wyolum/bebl_v2/kicad/data/conn_USB_cover_726291100.pdf

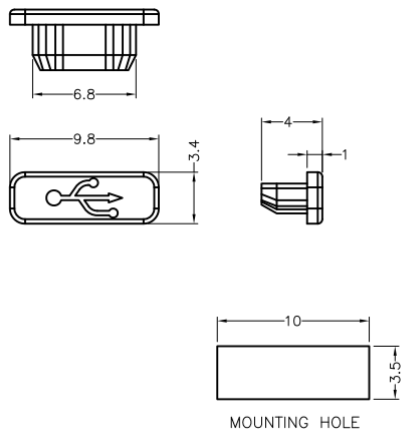
[picture p4: figure]

726291100 | Material: TPE
MICRO USB – Cover | Colour: black

Würth Elektronik eiSos GmbH & Co KG
D – 74638 Waldenburg
Max-Eyth-Straße 1
Tel.: 0049 7942-945-0 / Fax: 0049 7942-945-400

www.we-online.de
