wyolum/bebl_v2/kicad/images/bebl_v2_01.png

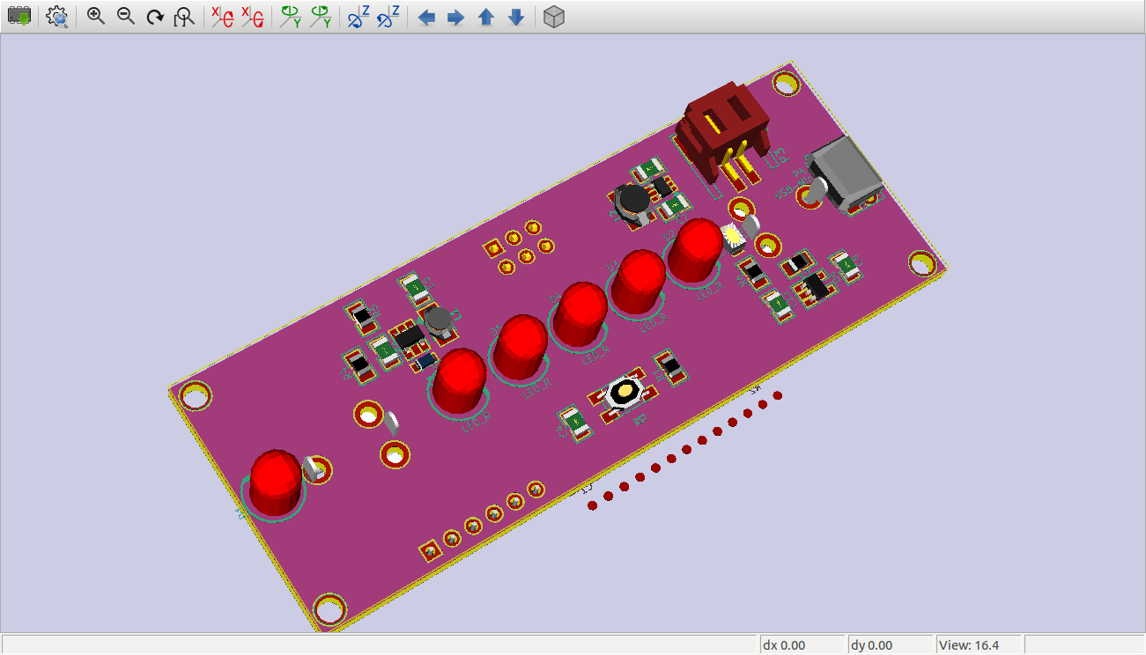
kicad/images/bebl_v2_01.png
