wyolum/bebl_v2/kicad/images/bebl_v2_02.png

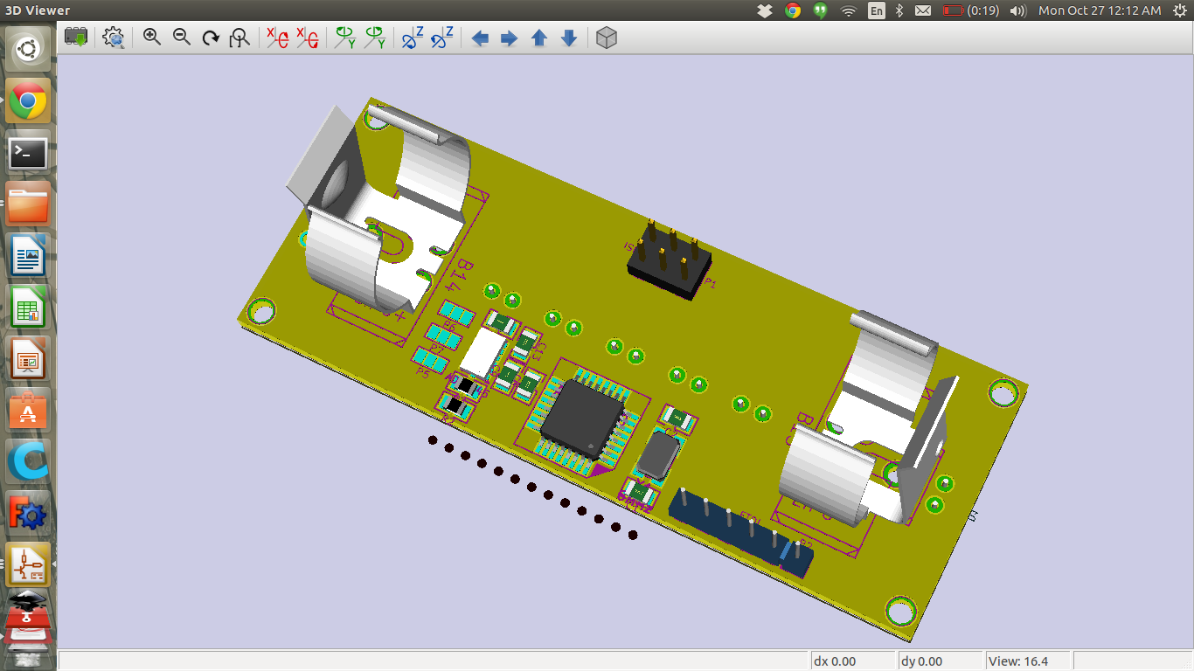
kicad/images/bebl_v2_02.png
