wyolum/bebl_v2/fabricate/old_archive/topcover.stl

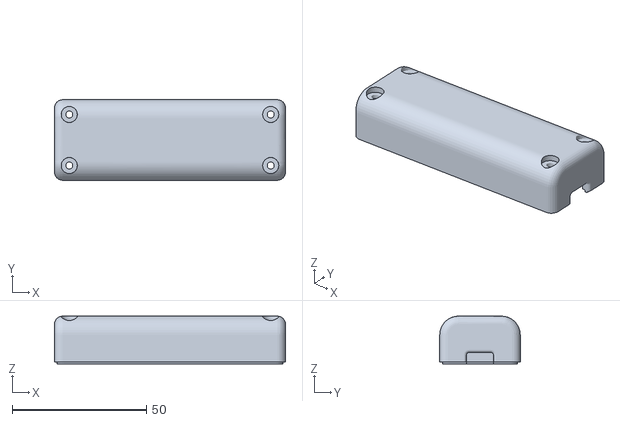
[picture p26: CAD file, 2014-11-03, an earlier design]
fabricate/old_archive/topcover.stl
86.0 x 30.0 x 17.8
