wyolum/bebl_v2/fabricate/bebl_v2_box03.png

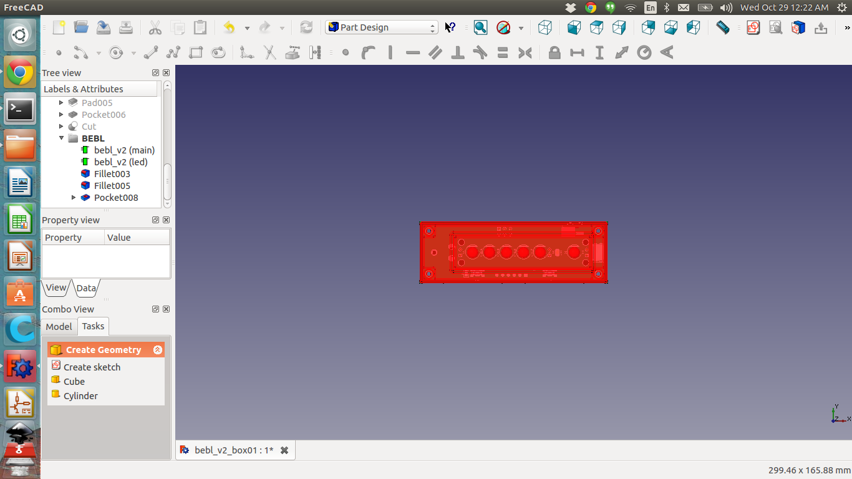
fabricate/bebl_v2_box03.png
