wyolum/bebl_v2/fabricate/bebl_v2_box4.png

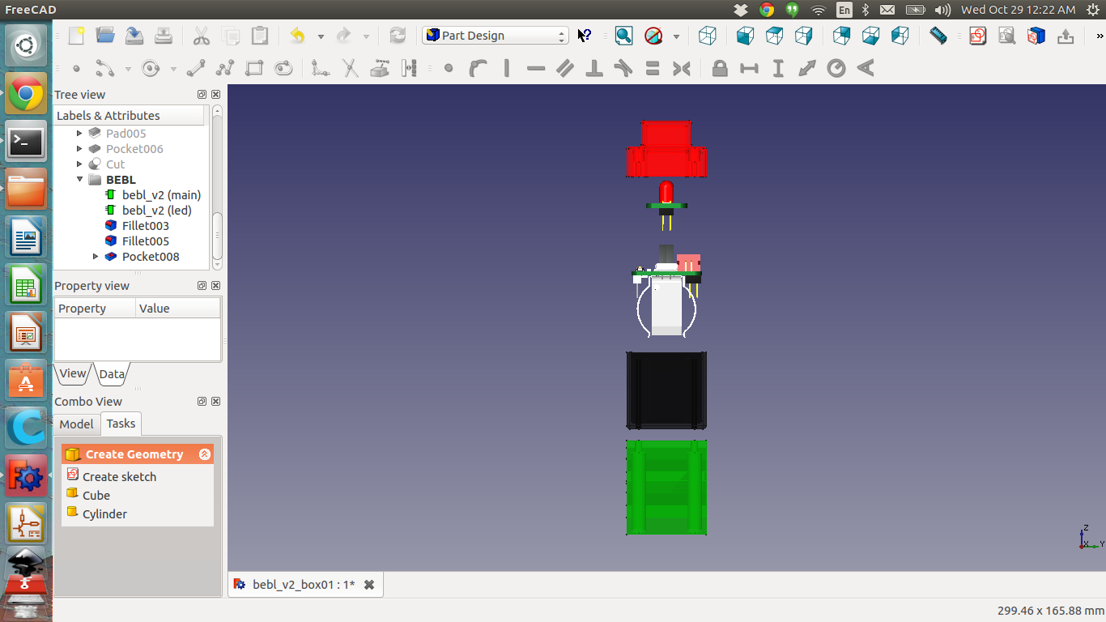
fabricate/bebl_v2_box4.png
