wyolum/bebl_v2/fabricate/bebl_v2_box05.png

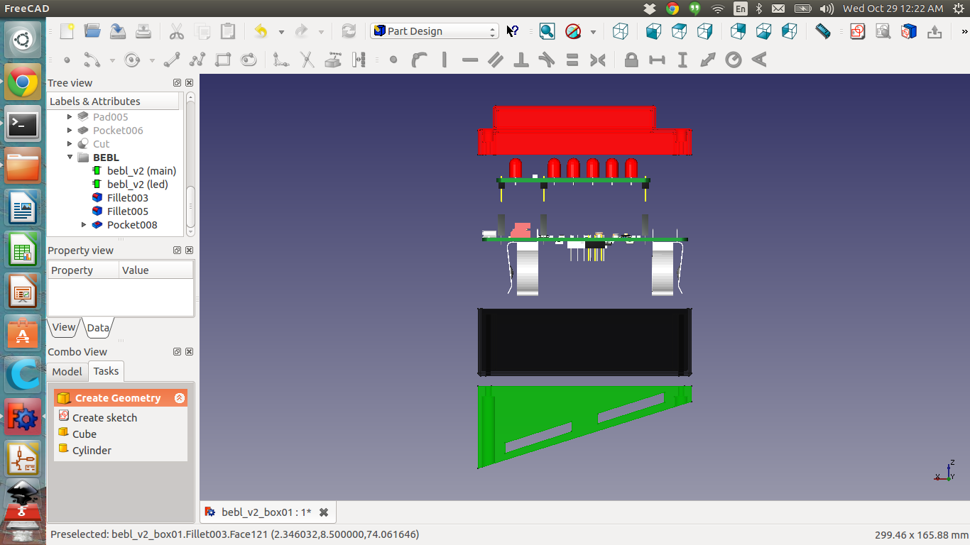
fabricate/bebl_v2_box05.png
