wyolum/bebl_v2/kicad/pdf/bebl_v2.pdf

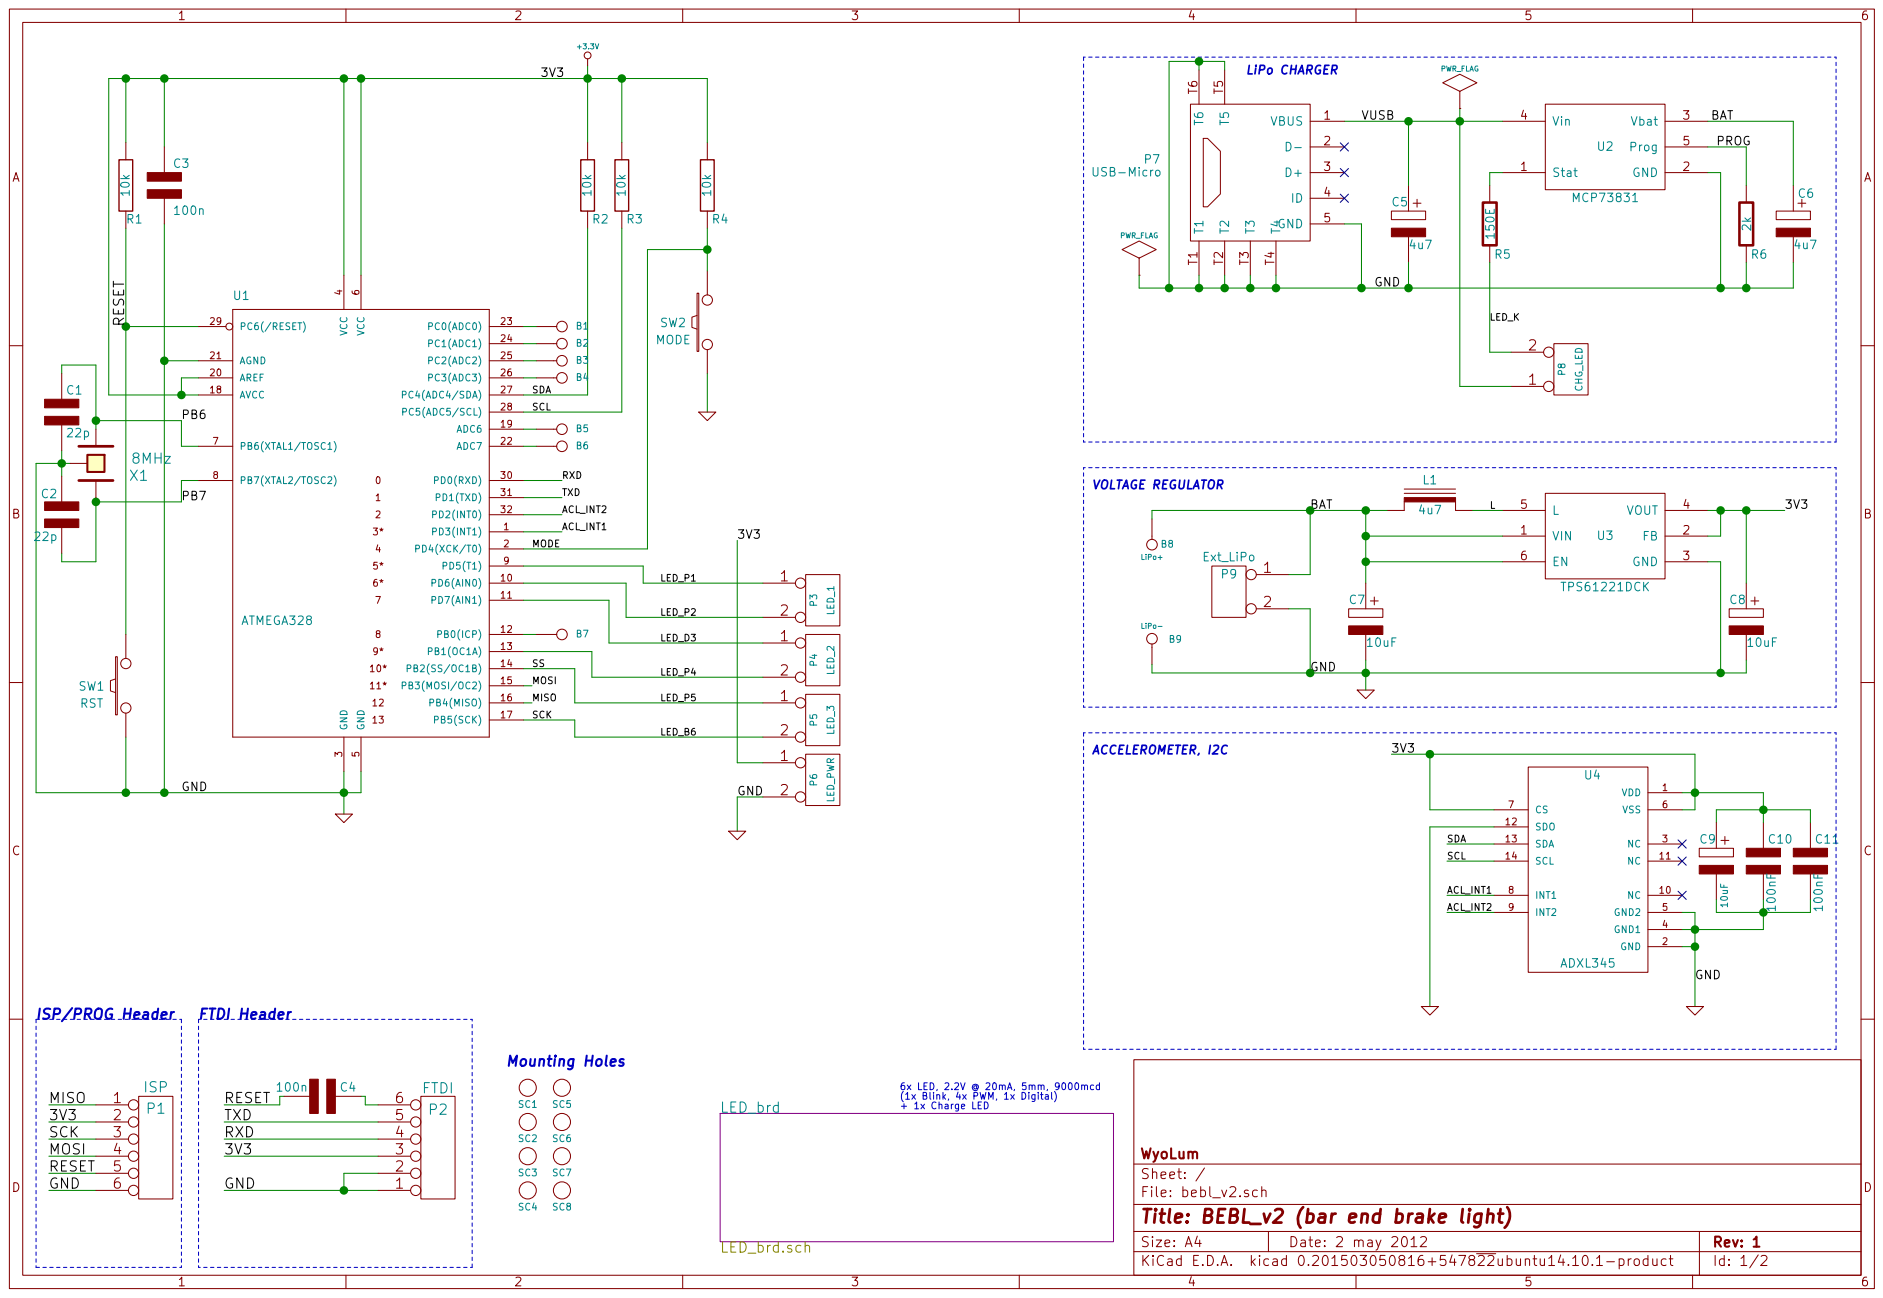
[picture p34: page 1]

6 PB6(XTAL1/TOSC1) 7 PB7(XTAL2/TOSC2) 8 PD5(T1) 9 PD6(AIN0) 10 AREF 20 PD0(RXD) 30 PD7(AIN1) 11 AGND 21 PD1(TXD) 31 PB0(ICP) 12 ADC7 22 PD2(INT0) 32 PB1(OC1A) 13 PC0(ADC0) 23 PB2(SS/OC1B) 14 PC1(ADC1) 24 PB3(MOSI/OC2) 15 PC2(ADC2) 25 PB4(MISO) 16 PC3(ADC3) 26 PB5(SCK) 17 PC4(ADC4/SDA) 27 AVCC 18 PC5(ADC5/SCL) 28 ADC6 19 PC6(/RESET) 29 U1ATMEGA328 X1

SDA
SCL SSMOSI SCK MISO

6x LED, 2.2V @ 20mA, 5mm, 9000mcd
(1x Blink, 4x PWM, 1x Digital) + 1x Charge LED

File: bebl_v2.sch Sheet: / WyoLum

Id: 1/2 Title: BEBL_v2 (bar end brake light)

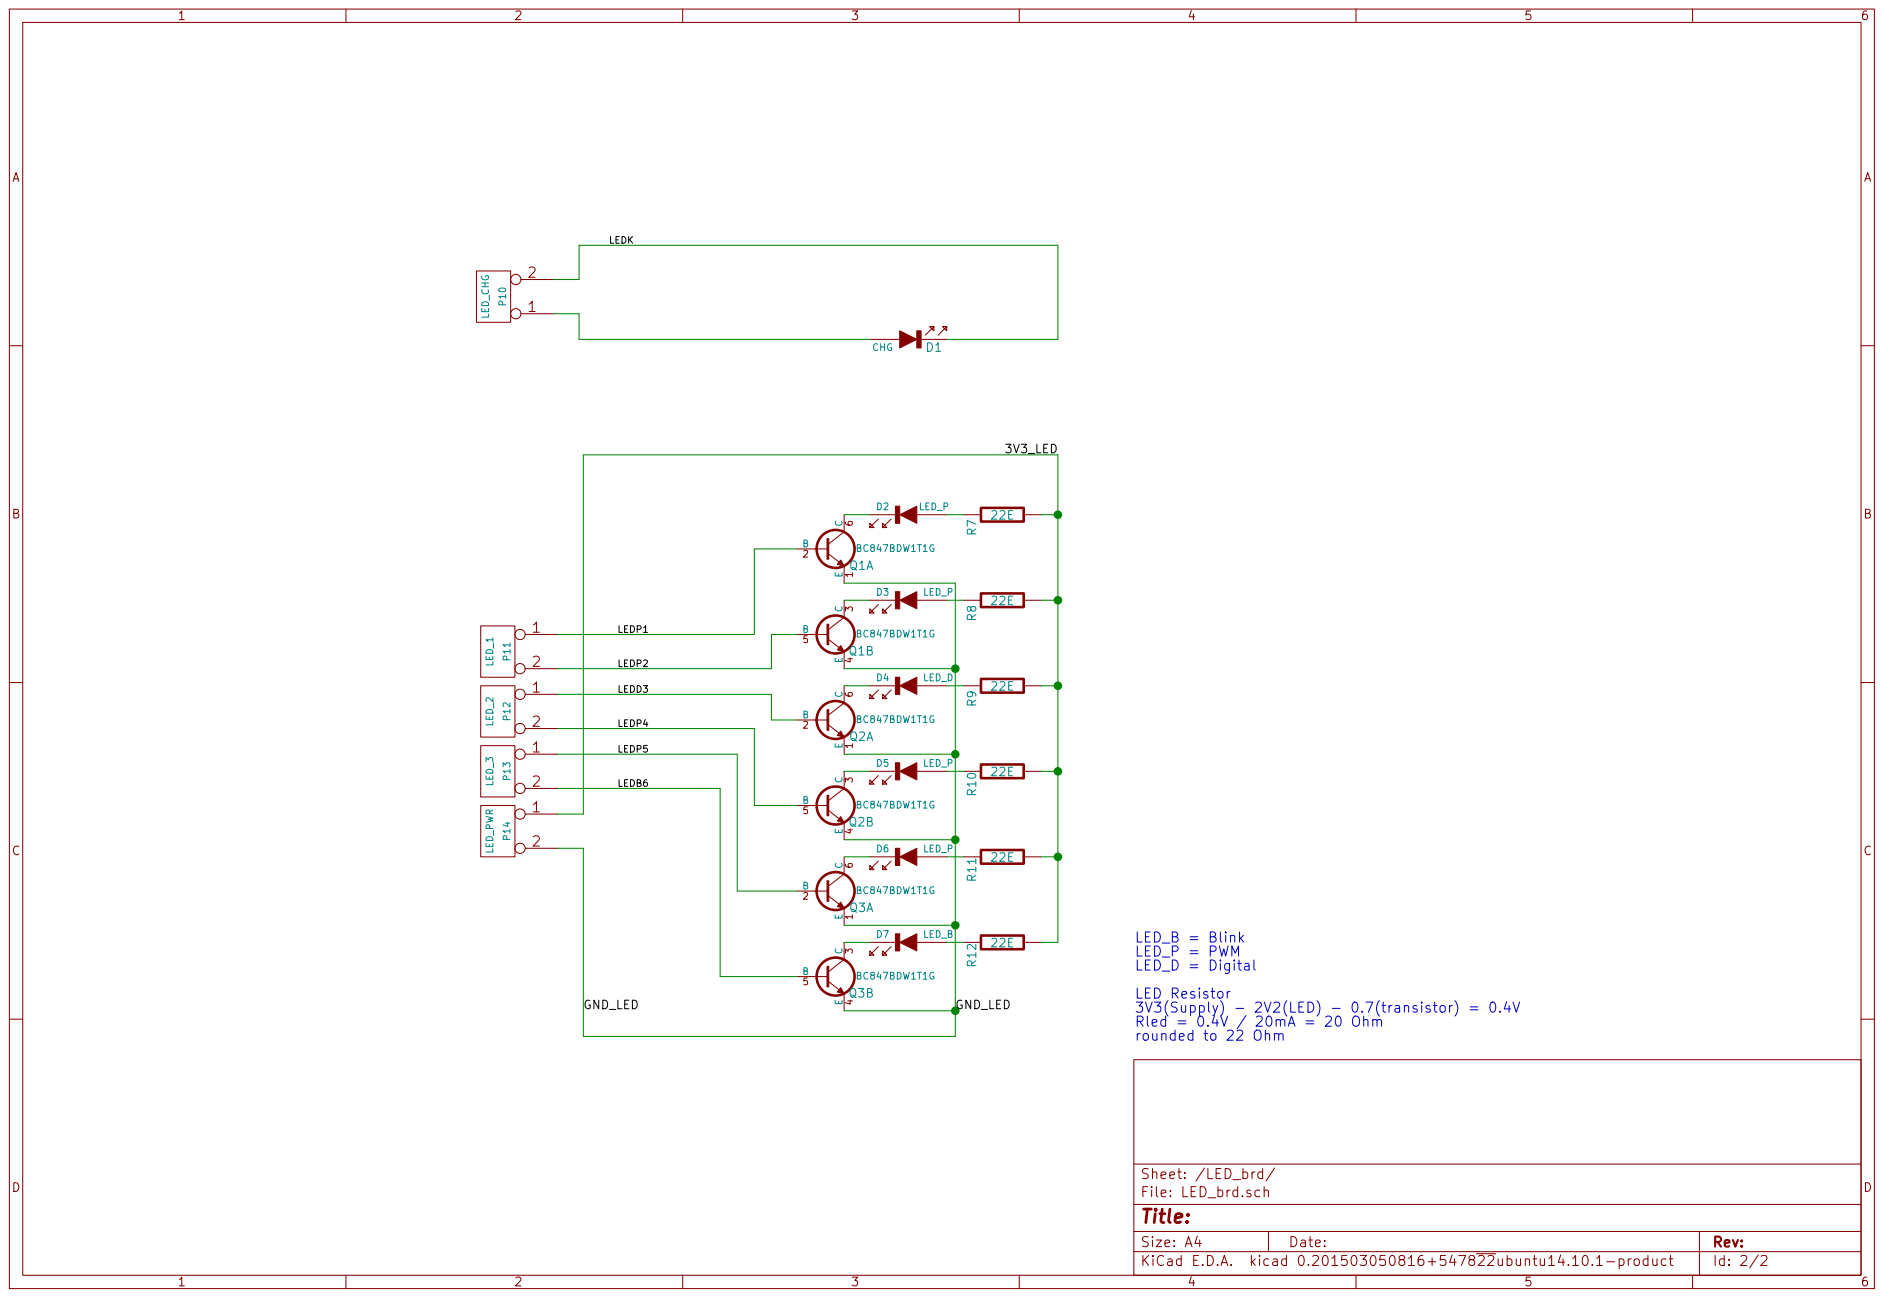
[picture p35: page 2]

LED_B = Blink
LED_P = PWM
LED_D = Digital LED Resistor 3V3(Supply) - 2V2(LED) - 0.7(transistor) = 0.4V Rled = 0.4V / 20mA = 20 Ohm
