wyolum/bebl_v2/kicad/images/bebl_v2_mockup_01.pdf

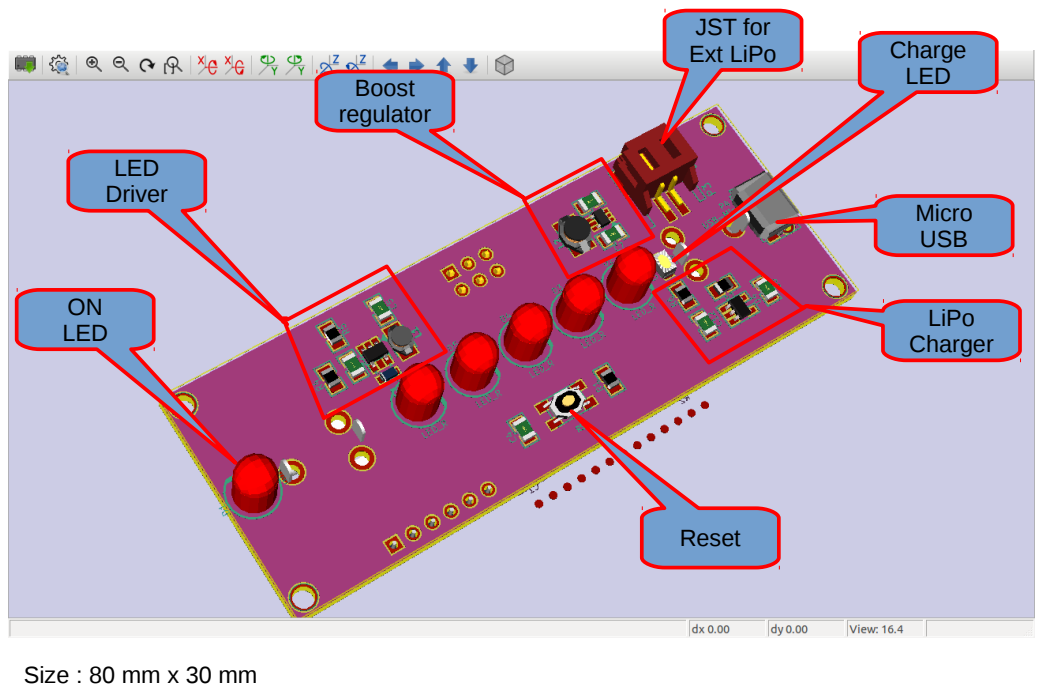
[picture p36: page 1]
LED Driver; Boost regulator; LiPo Charger; JST for Ext LiPo; Micro USB; Charge LED; ON LED; Reset

Size : 80 mm x 30 mm

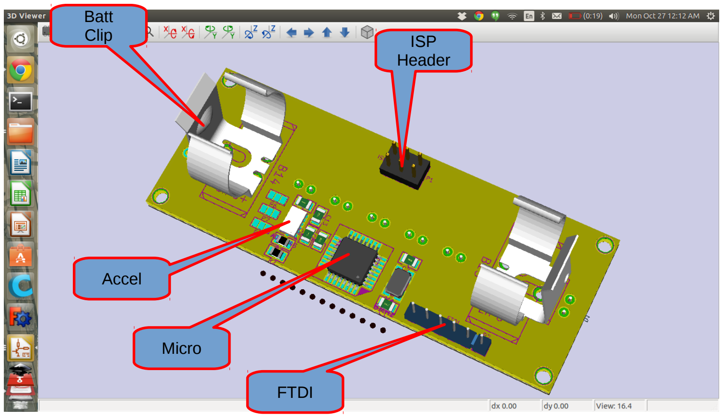
[picture p37: page 2]

Batt
Clip | ISP
| Header

Accel

Micro

FTDI
