wyolum/bebl_v2/kicad/pdf/bebl_v2-F_SilkS.pdf

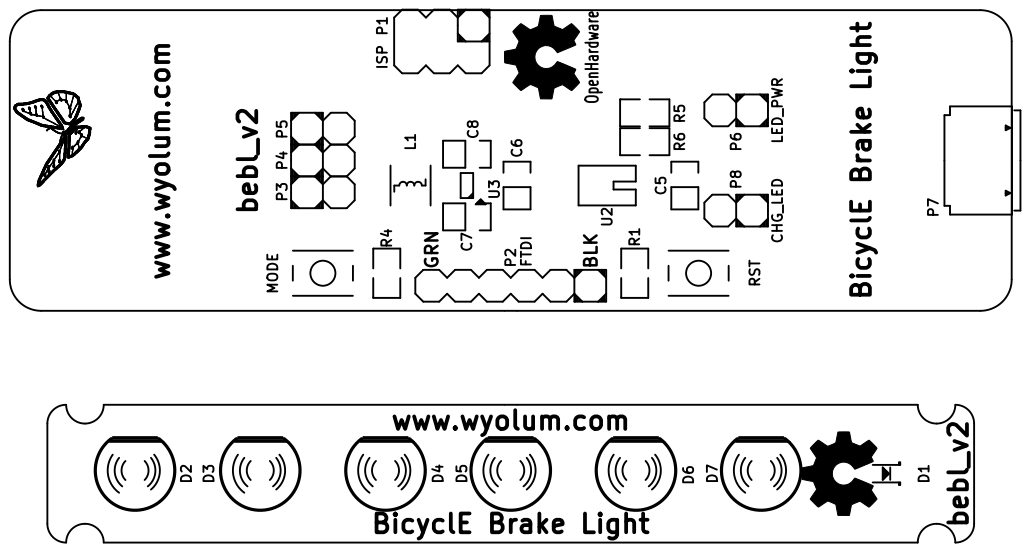
[picture p44: page 1]
