wyolum/bebl_v2/kicad/data/LED_Driver-LED_Driver.pdf

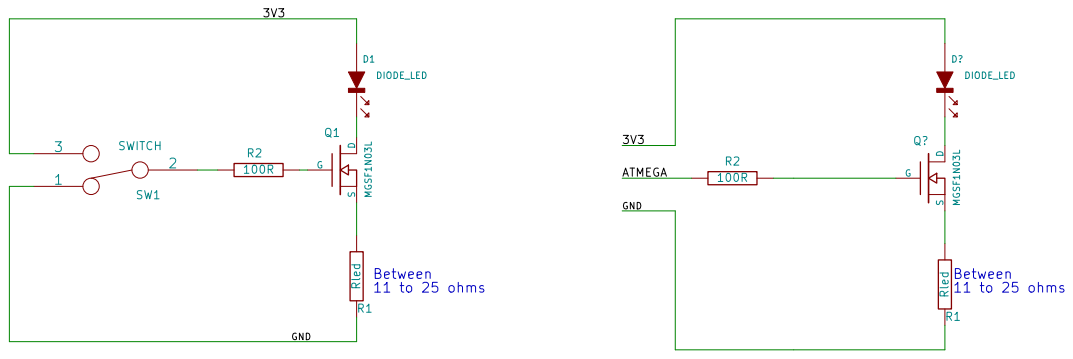
[picture p45: page 1]
