wyolum/bebl_v2/kicad/data/ADXL345_Breakout.pdf

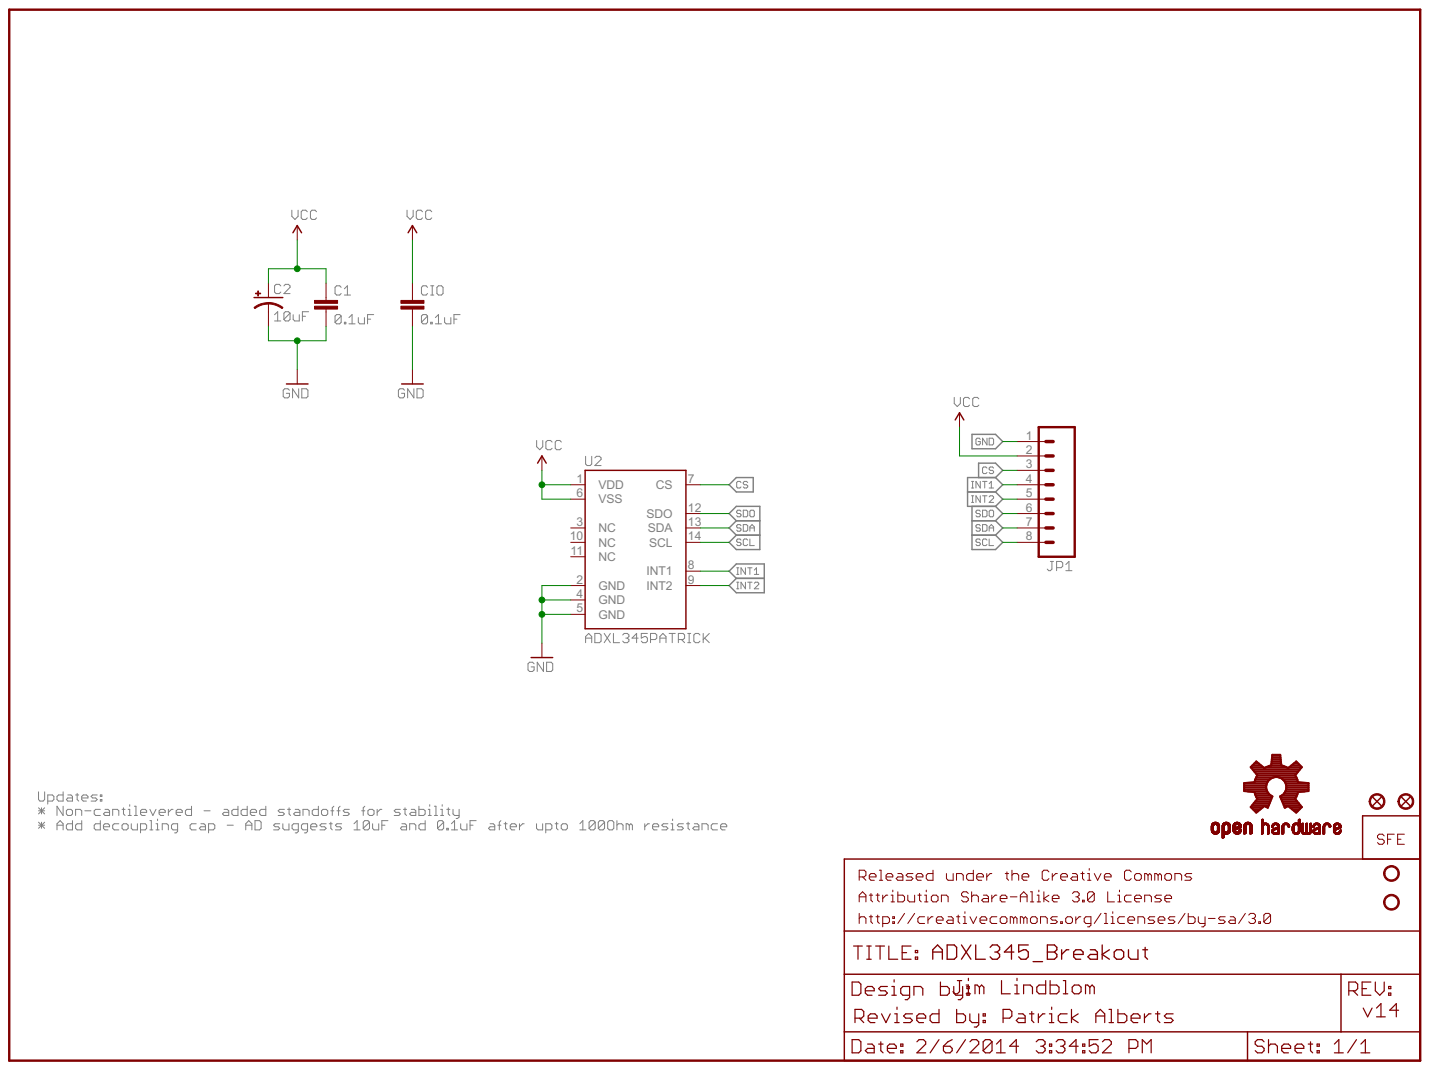
[picture p46: page 1]
